gallowayk/Graphene_openMiniITX/Images/Front.PNG

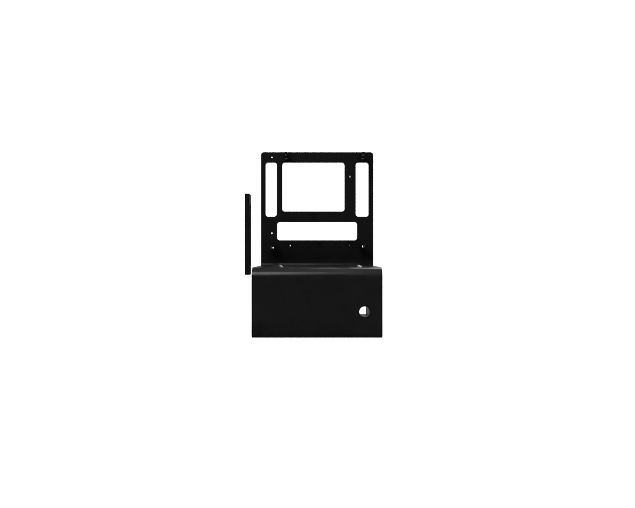
Images/Front.PNG
