gallowayk/Graphene_openMiniITX/History/v0_CaptureCard.jpg

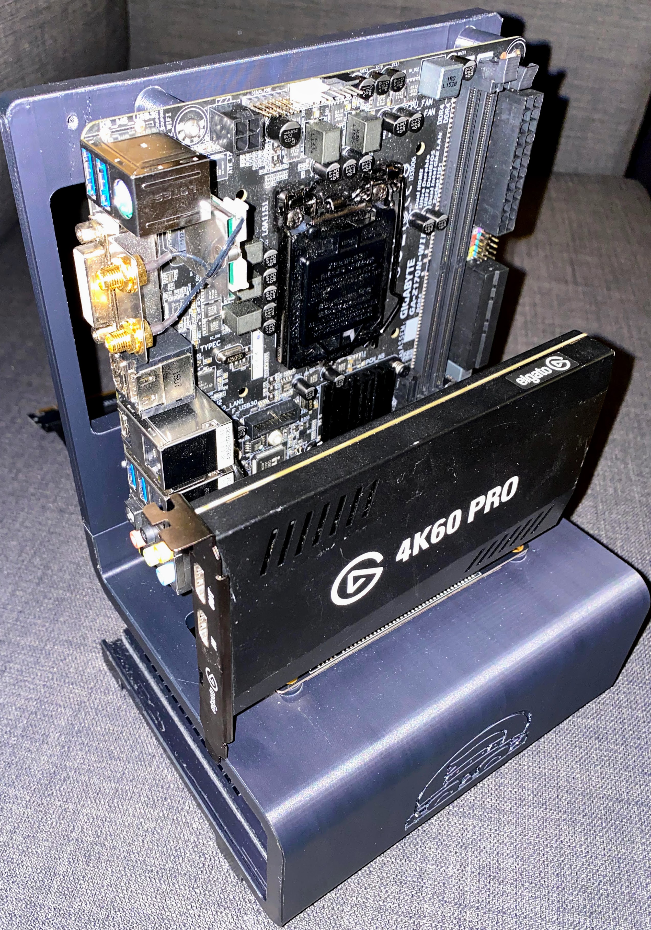
History/v0_CaptureCard.jpg
